delingren/jack-o-lantern/gallery/IMG_1635.jpeg

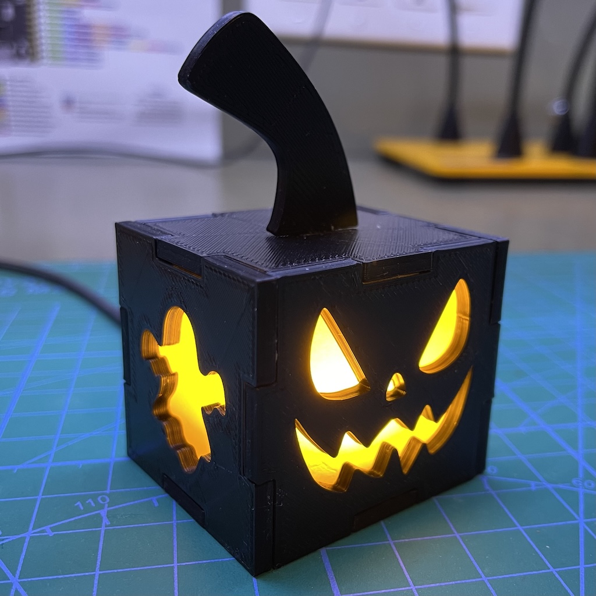
gallery/IMG_1635.jpeg
