delingren/jack-o-lantern/gallery/IMG_1637.jpeg

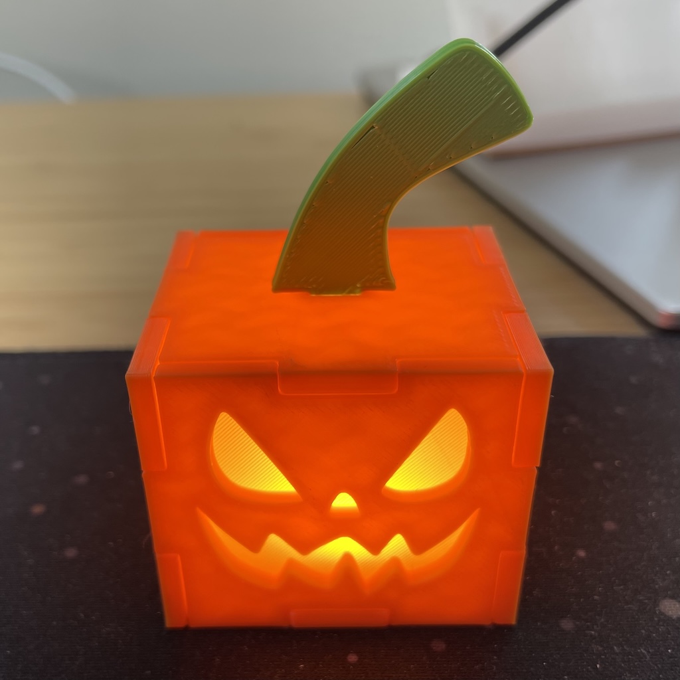
gallery/IMG_1637.jpeg
