delingren/jack-o-lantern/gallery/IMG_1645.jpeg

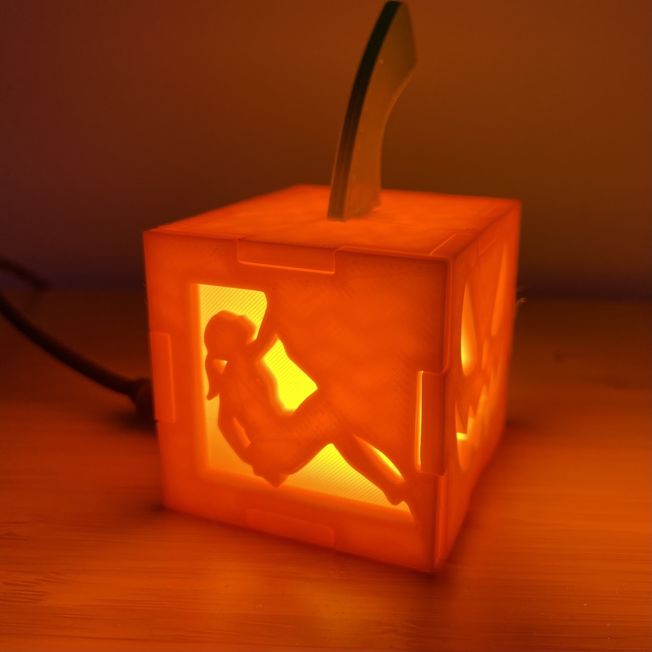
gallery/IMG_1645.jpeg
