delingren/jack-o-lantern/gallery/IMG_1652.jpeg

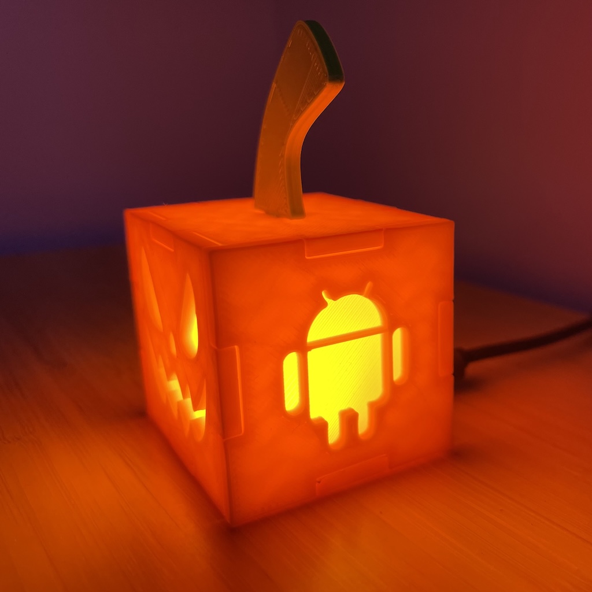
gallery/IMG_1652.jpeg
