delingren/jack-o-lantern/gallery/IMG_1653.jpeg

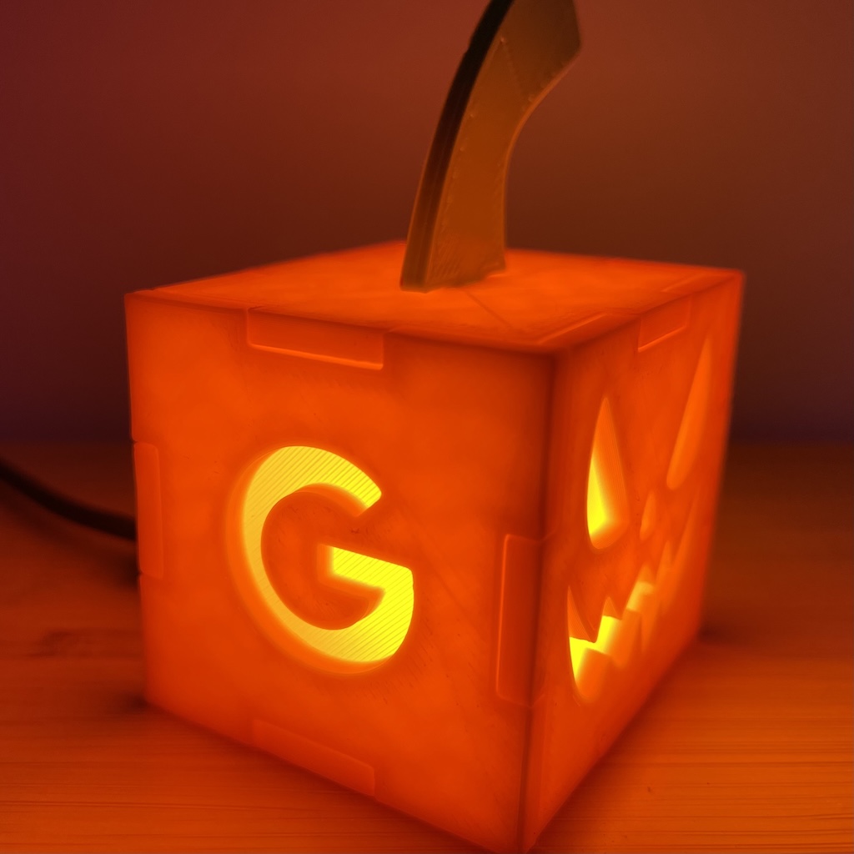
gallery/IMG_1653.jpeg
