delingren/jack-o-lantern/gallery/IMG_1655.jpeg

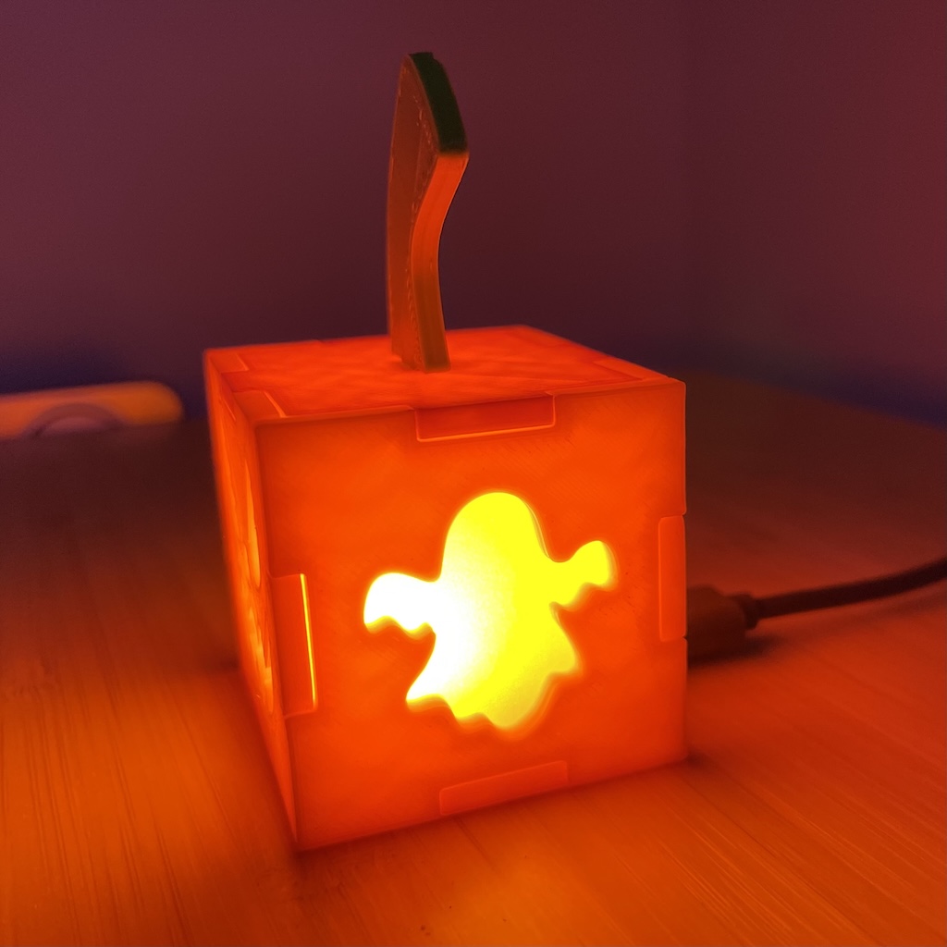
gallery/IMG_1655.jpeg
