delingren/jack-o-lantern/gallery/IMG_1656.jpeg

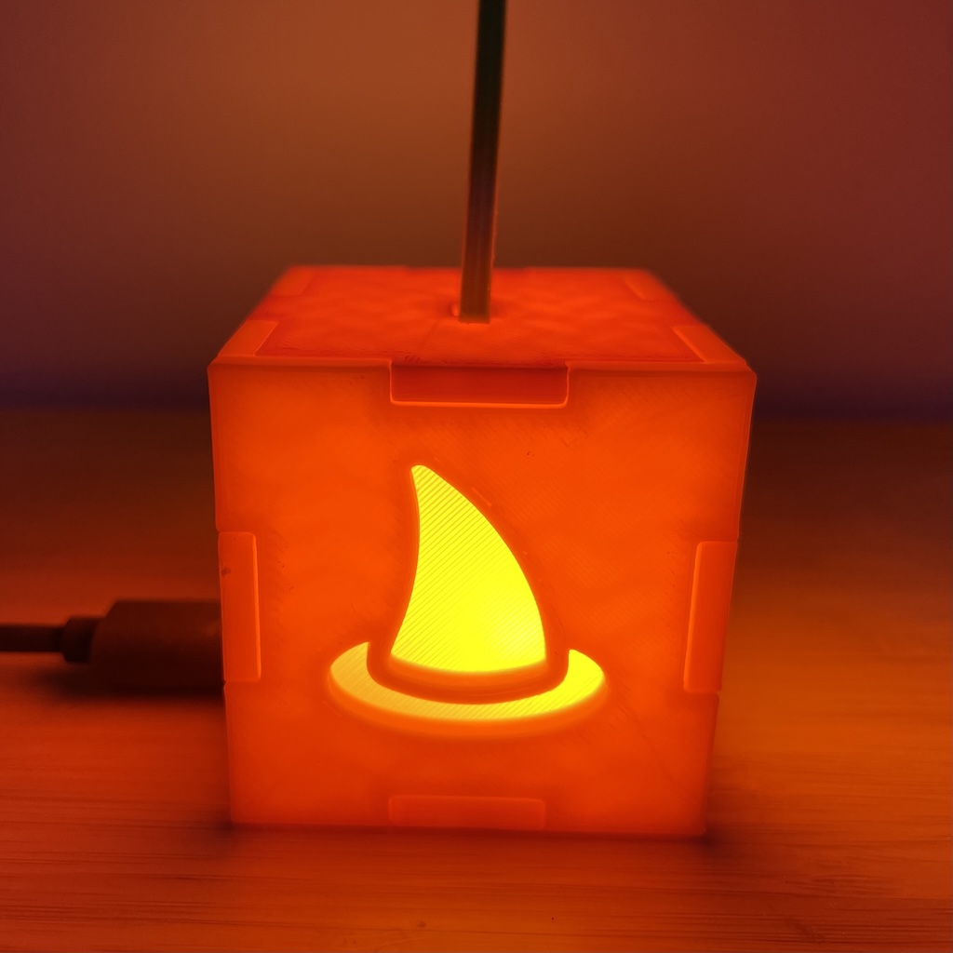
gallery/IMG_1656.jpeg
