delingren/jack-o-lantern/gallery/IMG_1657.jpeg

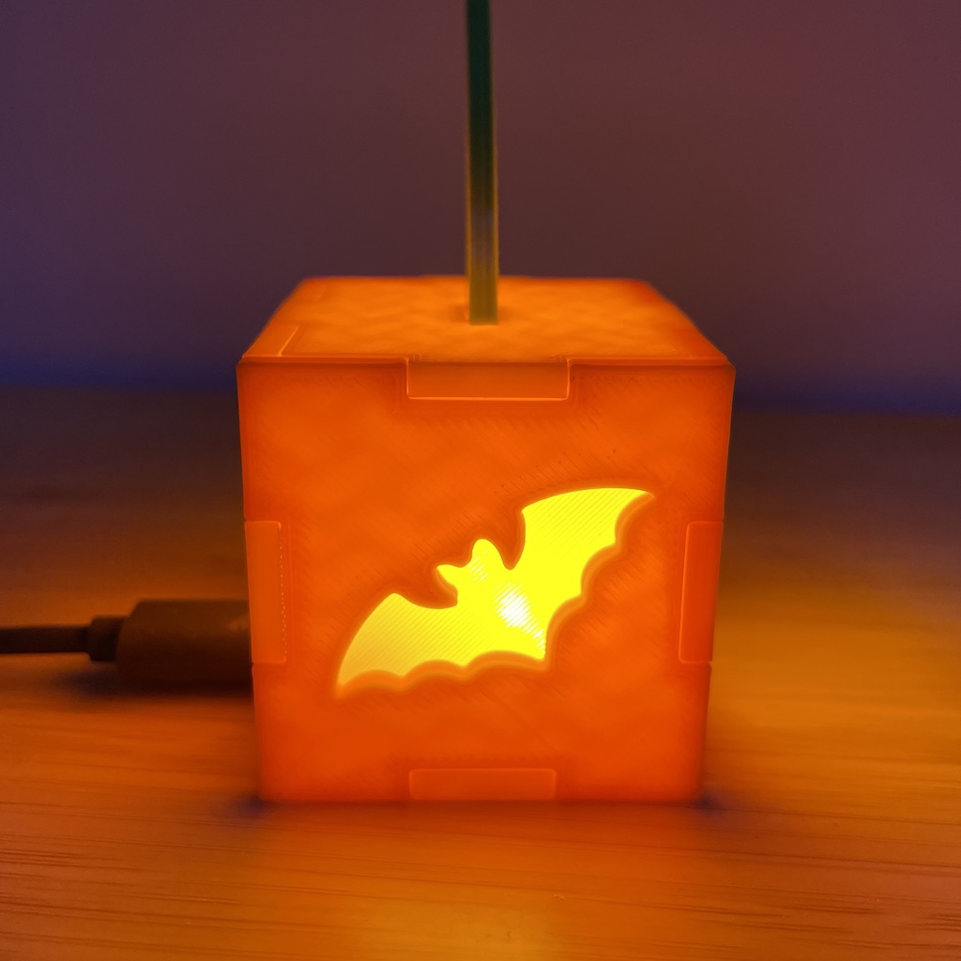
gallery/IMG_1657.jpeg
