delingren/jack-o-lantern/gallery/IMG_1665.jpeg

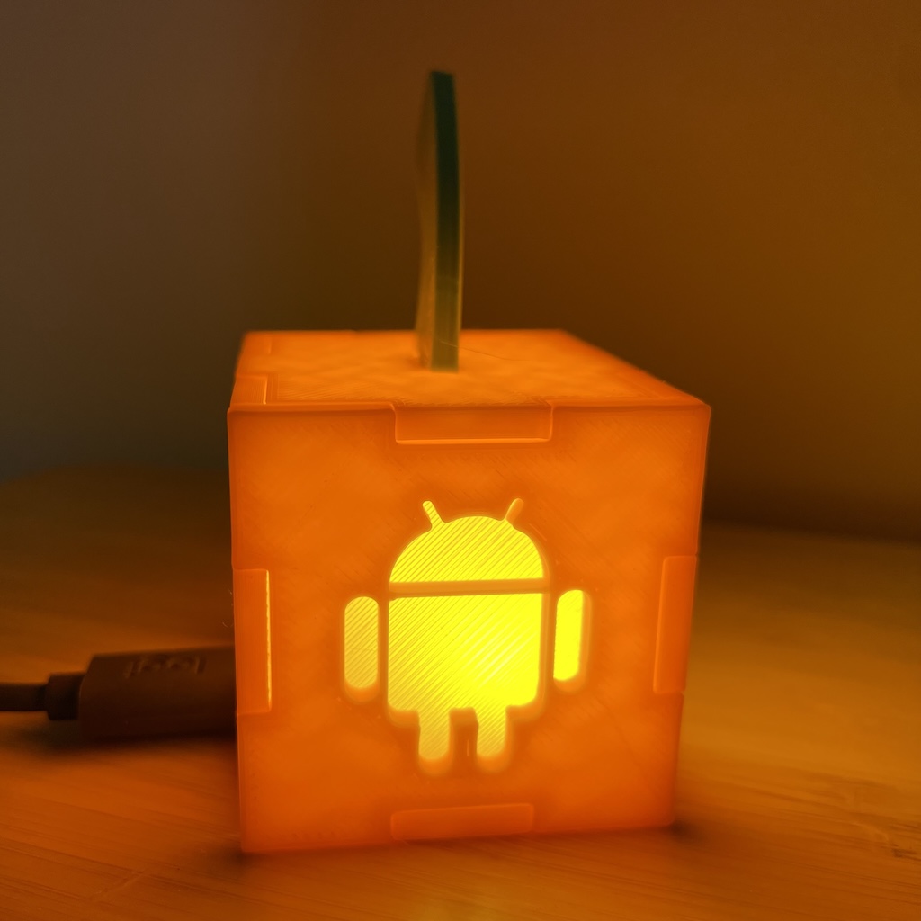
gallery/IMG_1665.jpeg
