delingren/jack-o-lantern/gallery/IMG_1666.jpeg

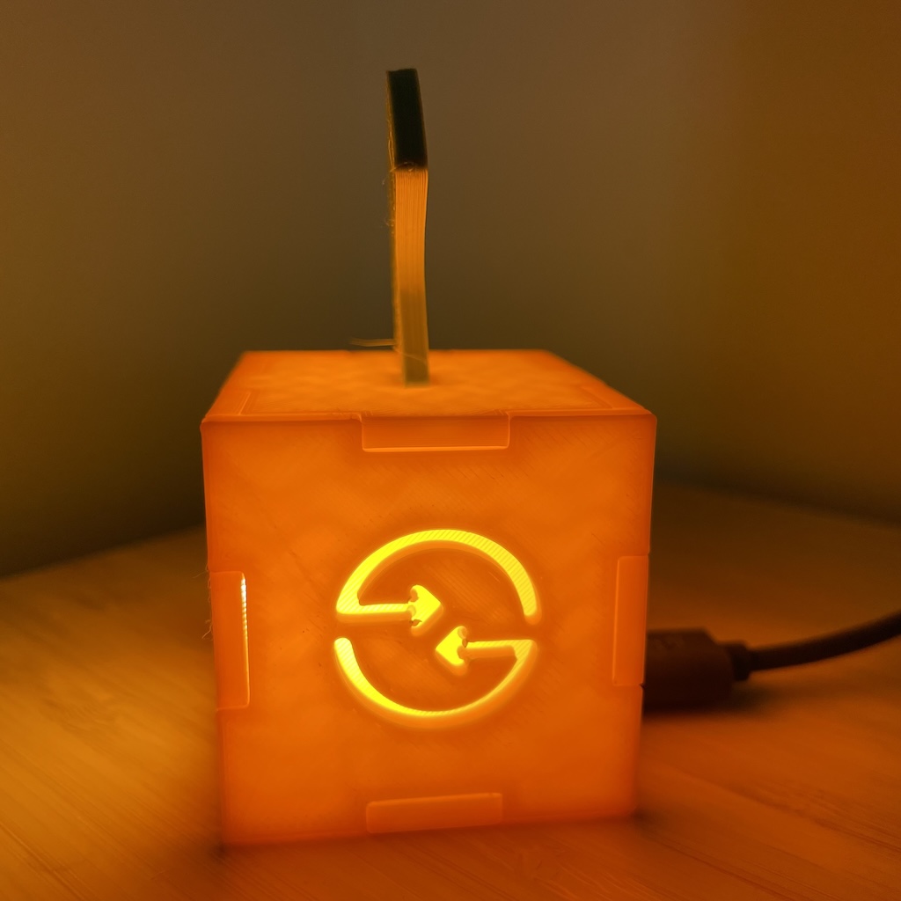
gallery/IMG_1666.jpeg
