delingren/jack-o-lantern/stls/black/top.stl

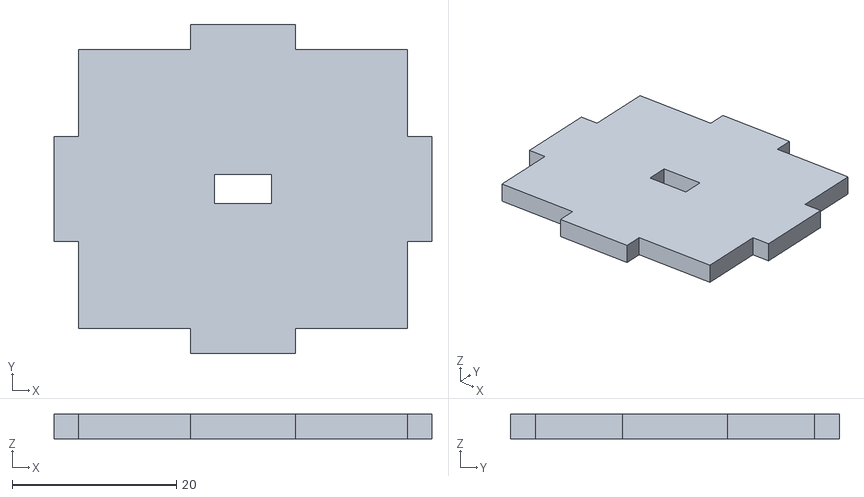
[picture p30: CAD file, 2025-10-05]
stls/black/top.stl
46.0 x 40.0 x 3.00
