delingren/jack-o-lantern/stls/black/ghost-2.stl

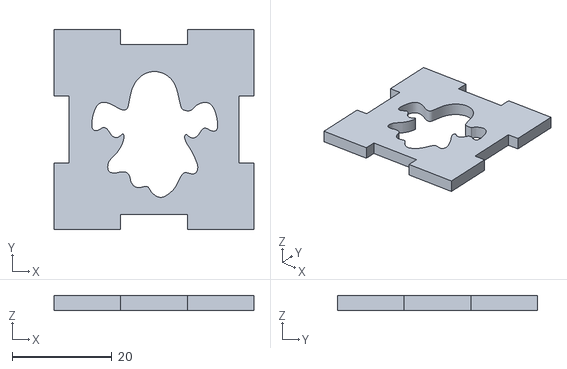
[picture p31: CAD file, 2025-10-03]
stls/black/ghost-2.stl
40.0 x 40.0 x 3.00
