delingren/jack-o-lantern/stls/orange/climber.stl

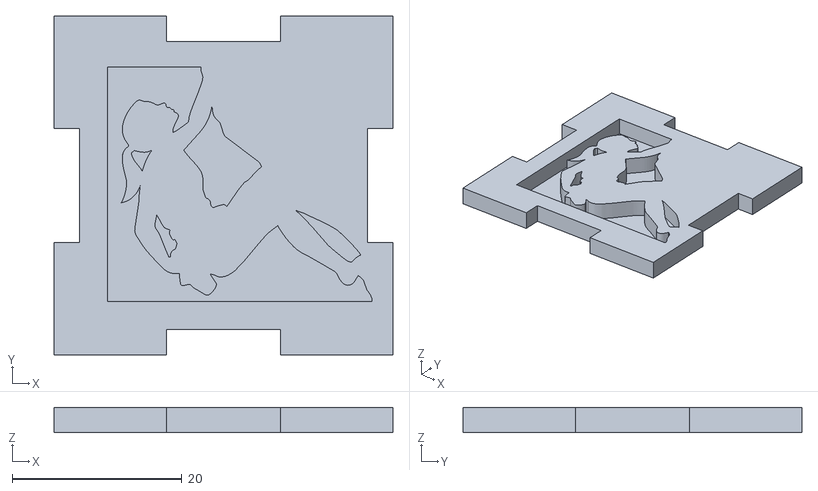
[picture p32: CAD file, 2025-10-07]
stls/orange/climber.stl
40.0 x 40.0 x 3.00
