delingren/jack-o-lantern/stls/black/back.stl

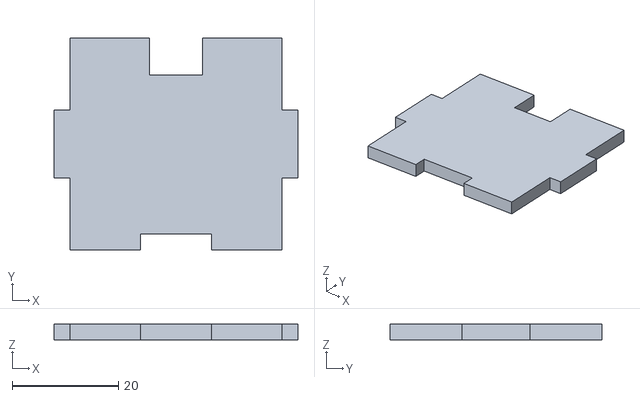
[picture p33: CAD file, 2025-10-03]
stls/black/back.stl
46.0 x 40.0 x 3.00
