delingren/jack-o-lantern/stls/orange/face.stl

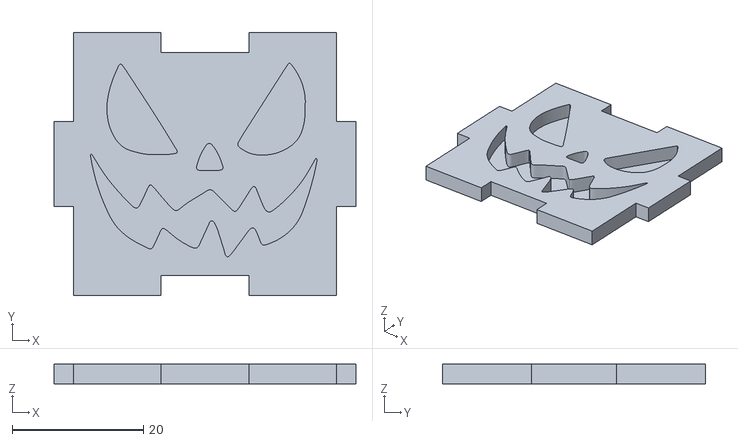
[picture p34: CAD file, 2025-10-04]
stls/orange/face.stl
46.0 x 40.0 x 3.00
